OneTwoZzzPlus/chicken/Color/Color_scheme1.png

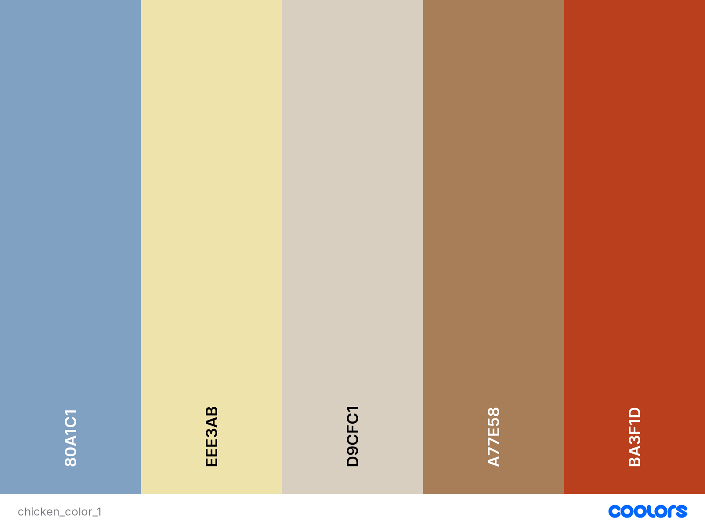
Color/Color_scheme1.png
