OneTwoZzzPlus/chicken/Pictures/es.jpg

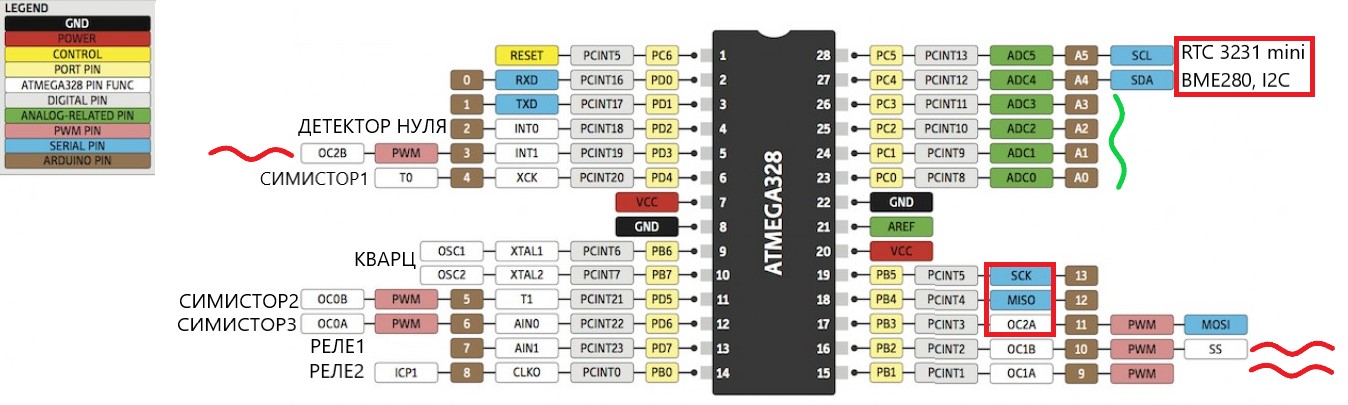
Pictures/es.jpg
