OneTwoZzzPlus/chicken/Pictures/esp8266.png

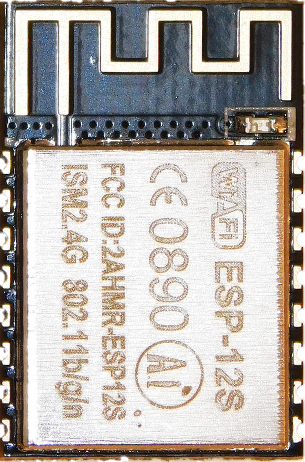
Pictures/esp8266.png
