OneTwoZzzPlus/chicken/Pictures/PCB-full/3d.png

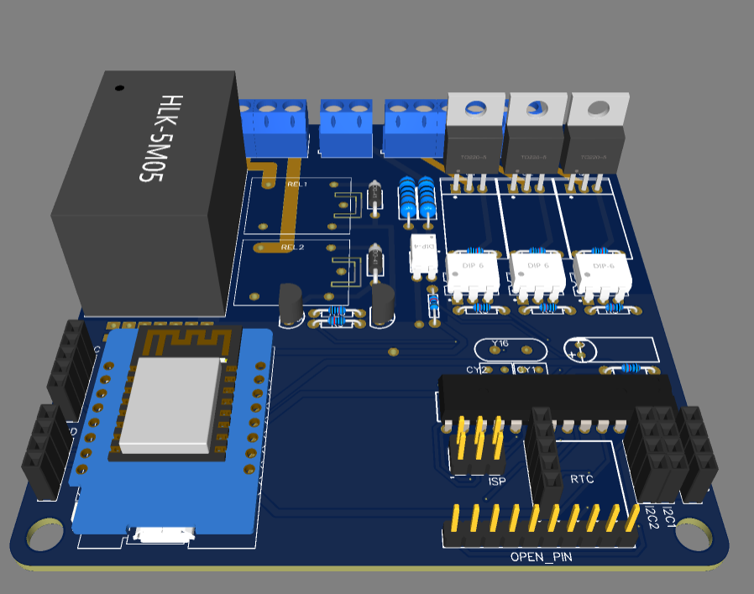
Pictures/PCB-full/3d.png
