OneTwoZzzPlus/chicken/Pictures/Photos/20230208_175712.jpg

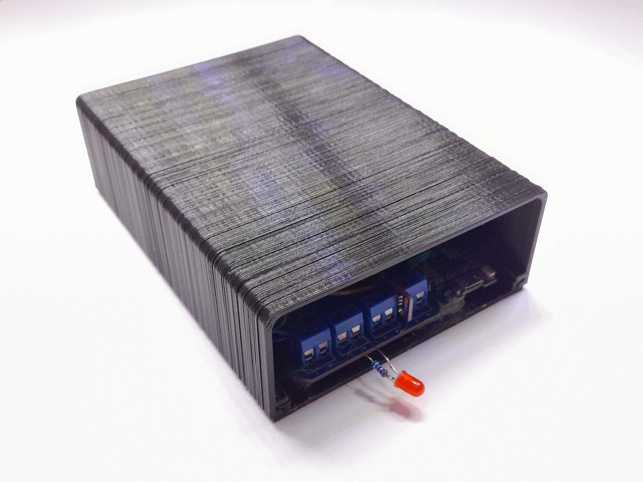
Pictures/Photos/20230208_175712.jpg
