OneTwoZzzPlus/chicken/Pictures/Photos/20230208_175812.jpg

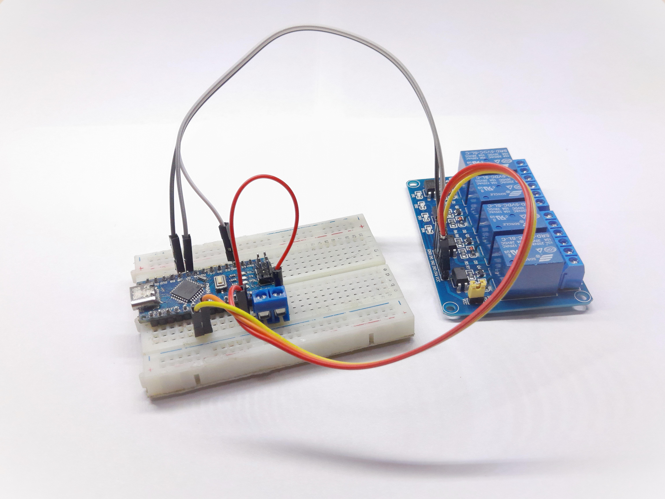
Pictures/Photos/20230208_175812.jpg
