OneTwoZzzPlus/chicken/Pictures/Photos/20230208_175840.jpg

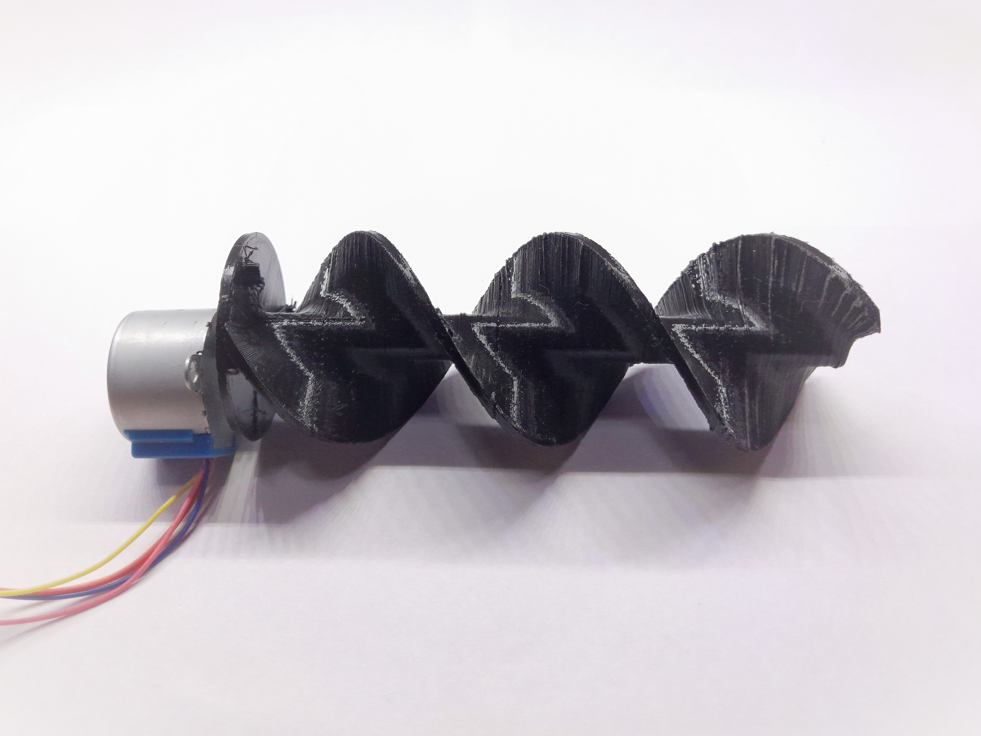
Pictures/Photos/20230208_175840.jpg
