OneTwoZzzPlus/chicken/Pictures/Photos/20230208_180006.jpg

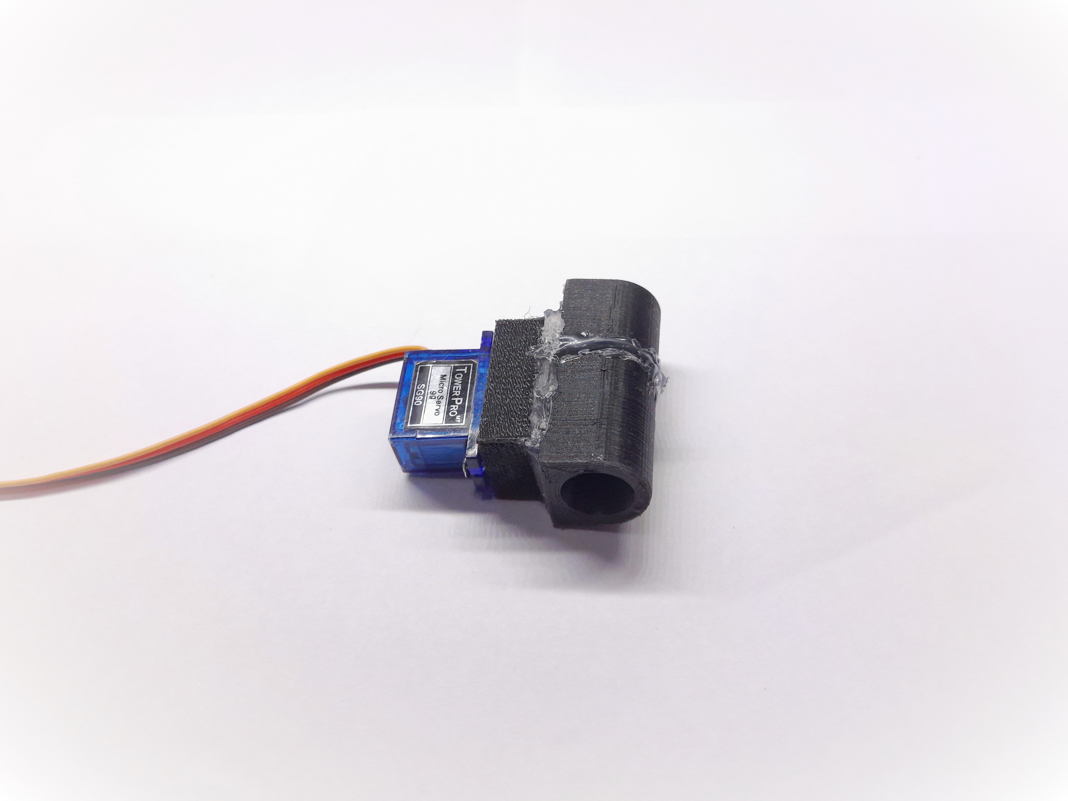
Pictures/Photos/20230208_180006.jpg
